koendv/retroleds/arduino/retroleds/glcdfont.h

#ifndef FONT5X7_H
#define FONT5X7_H

#include <Arduino.h>

/*
 * 5x7 bitmap font for LCD devices. ascii, extended ascii, katakana, cyrillic. Total size 3.5kbyte.
 * Each character occupies 7 bytes. Each byte represents a row of 5 pixels.
 *
 * Each code page (ascii, extended ascii, katakana, cyrillic) contains 128 characters.
 * Character codes less than 128 are retrieved from the first code page (ascii). 
 * Character codes of 128 or higher are retrieved from extended ascii if the current font is 0, 
 * from katakana if the current font is 1, and from cyrillic if the current font is 2.
 *
 * If you add a code page increase MAX_FONTS.
 *
 * Do not exceed 20 illuminated pixels per character. This avoids thermal problems. 
 *
 */

static const uint8_t PROGMEM font[] = {

  // standard ascii
  
  0b00000,
  0b00000,
  0b00000,
  0b00000,
  0b00000,
  0b00000,
  0b00000,
  
  0b00000,
  0b00000,
  0b00000,
  0b00000,
  0b00000,
  0b00000,
  0b00000,
  
  0b00000,
  0b00000,
  0b00000,
  0b00000,
  0b00000,
  0b00000,
  0b00000,
  
  0b00000,
  0b00000,
  0b00000,
  0b00000,
  0b00000,
  0b00000,
  0b00000,
  
  0b00000,
  0b00000,
  0b00000,
  0b00000,
  0b00000,
  0b00000,
  0b00000,
  
  0b00000,
  0b00000,
  0b00000,
  0b00000,
  0b00000,
  0b00000,
  0b00000,
  
  0b00000,
  0b00000,
  0b00000,
  0b00000,
  0b00000,
  0b00000,
  0b00000,
  
  0b00000,
  0b00000,
  0b00000,
  0b00000,
  0b00000,
  0b00000,
  0b00000,
  
  0b00000,
  0b00000,
  0b00000,
  0b00000,
  0b00000,
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
  0b11110,
  0b10001,
  0b11110,
  
  0b00000,
  0b00000,
  0b01110,
  0b10001,
  0b00111,
  0b10001,
  0b01110,
  
  0b00000,
  0b00000,
  0b10010,
  0b10101,
  0b11101,
  0b10101,
  0b10010,
  
  0b00000,
  0b00000,
  0b01111,
  0b10001,
  0b01111,
  0b01001,
  0b10001,

};
#endif // FONT5X7_H
